ChristianIannella/OneDigitDisplay/Media/IMG_0269.jpg

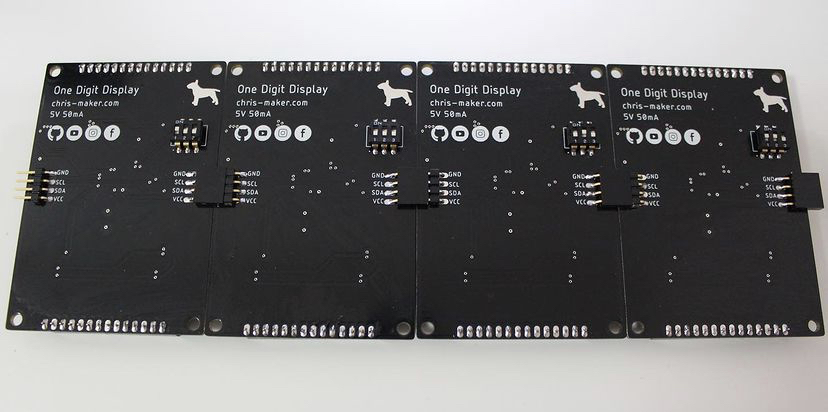
Media/IMG_0269.jpg
